huzmo/HuzDSP/Firmware/Drivers/lvgl-release-v9.5/docs/src/_static/images/clip_corner_3_layers_created.png

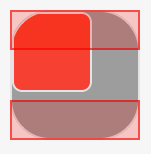
Firmware/Drivers/lvgl-release-v9.5/docs/src/_static/images/clip_corner_3_layers_created.png
