huzmo/HuzDSP/Firmware/Drivers/lvgl-release-v9.5/docs/src/_static/images/editor_initial_ui.png

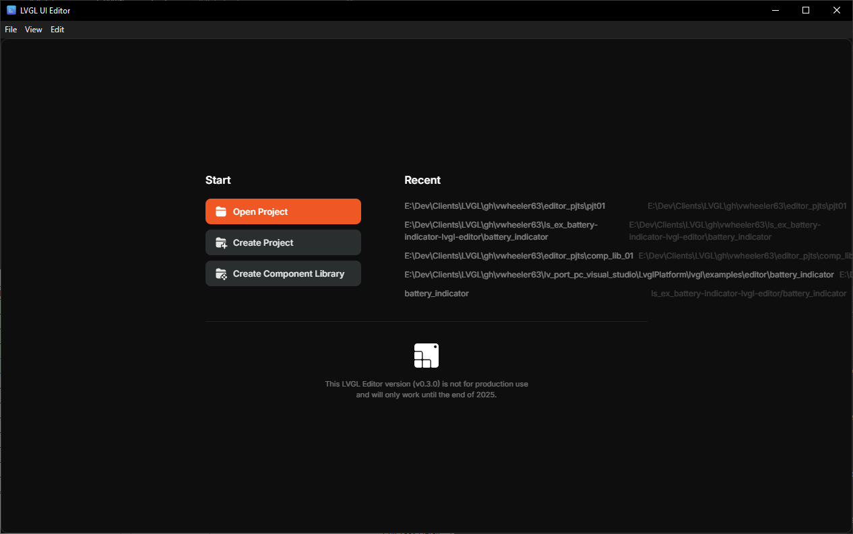
Firmware/Drivers/lvgl-release-v9.5/docs/src/_static/images/editor_initial_ui.png
