huzmo/HuzDSP/Firmware/Drivers/lvgl-release-v9.5/docs/src/_static/images/figma_to_lvgl_menu.png

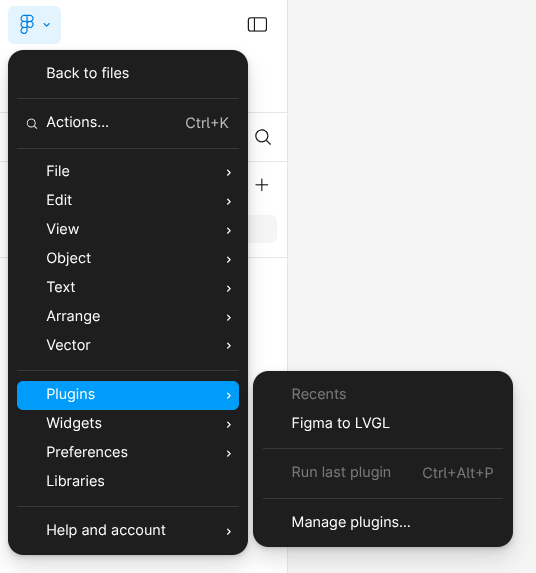
Firmware/Drivers/lvgl-release-v9.5/docs/src/_static/images/figma_to_lvgl_menu.png
