huzmo/HuzDSP/Firmware/Drivers/lvgl-release-v9.5/docs/src/_static/images/figma_to_lvgl_plugin.png

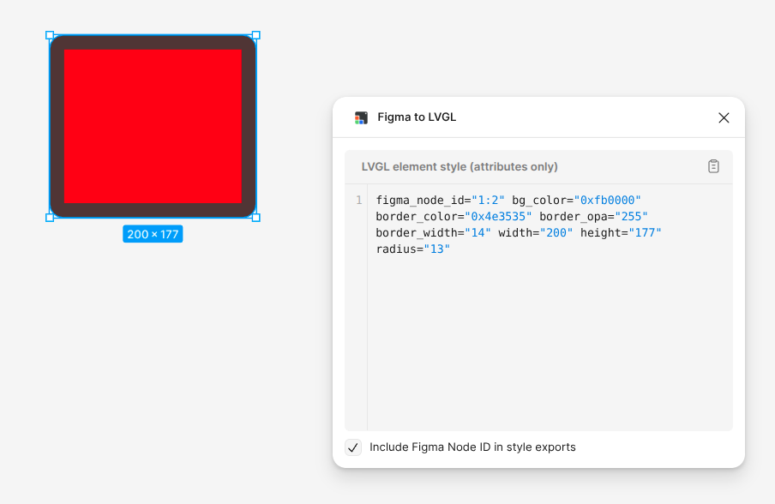
Firmware/Drivers/lvgl-release-v9.5/docs/src/_static/images/figma_to_lvgl_plugin.png
