huzmo/HuzDSP/Firmware/Drivers/lvgl-release-v9.5/docs/src/_static/images/gh-header.webp

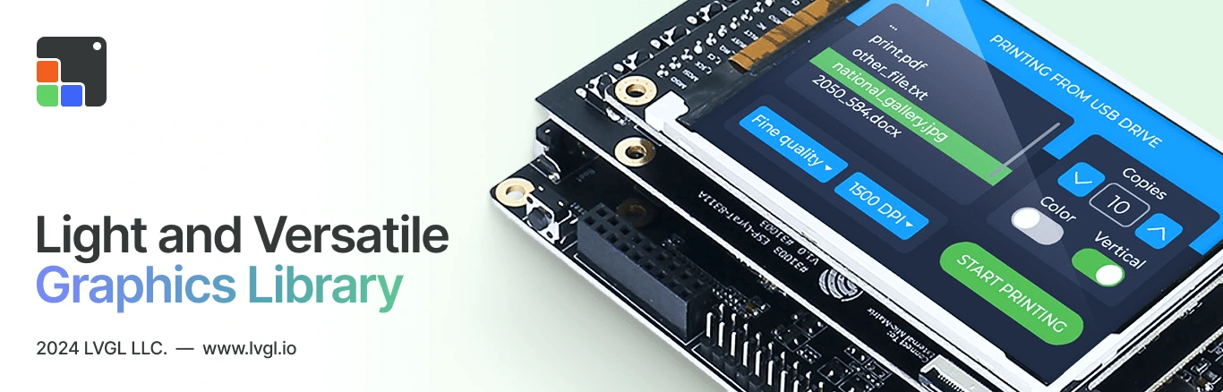
Firmware/Drivers/lvgl-release-v9.5/docs/src/_static/images/gh-header.webp
