huzmo/HuzDSP/Firmware/Drivers/lvgl-release-v9.5/docs/src/_static/images/home_1.png

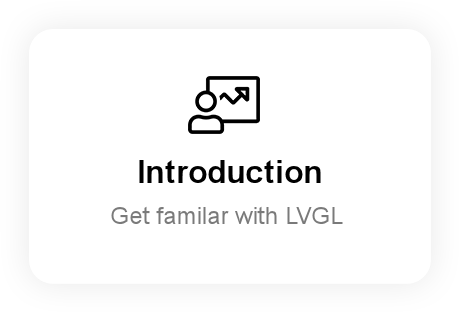
Firmware/Drivers/lvgl-release-v9.5/docs/src/_static/images/home_1.png
