huzmo/HuzDSP/Firmware/Drivers/lvgl-release-v9.5/docs/src/_static/images/home_3.png

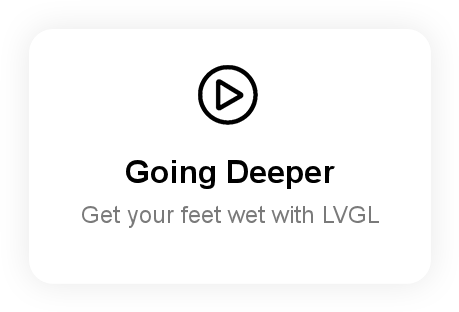
Firmware/Drivers/lvgl-release-v9.5/docs/src/_static/images/home_3.png
