huzmo/HuzDSP/Firmware/Drivers/lvgl-release-v9.5/docs/src/_static/images/intro_data_flow.png

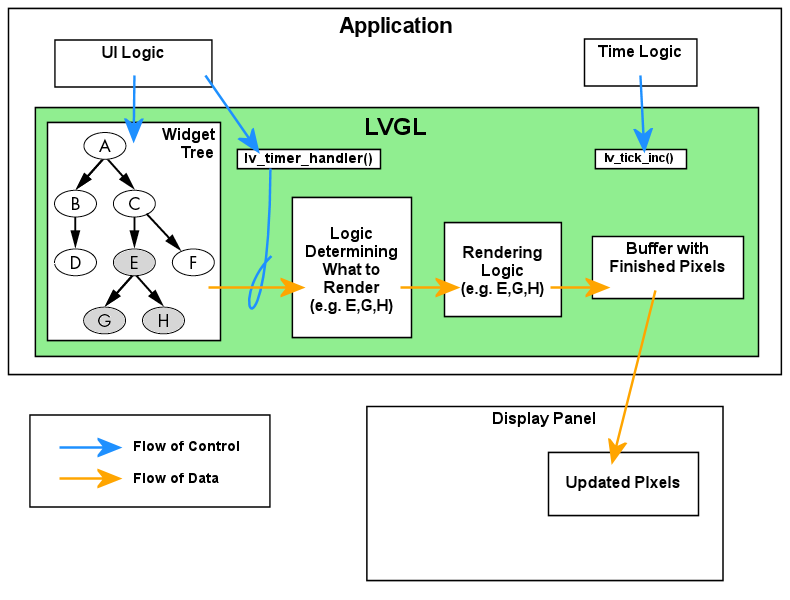
Firmware/Drivers/lvgl-release-v9.5/docs/src/_static/images/intro_data_flow.png
