huzmo/HuzDSP/Firmware/Drivers/lvgl-release-v9.5/docs/src/_static/images/lz4-compress-statistics.png

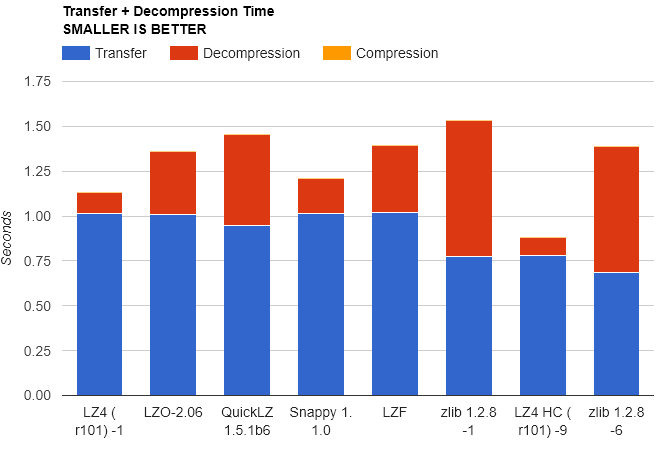
Firmware/Drivers/lvgl-release-v9.5/docs/src/_static/images/lz4-compress-statistics.png
