huzmo/HuzDSP/Firmware/Drivers/lvgl-release-v9.5/docs/src/_static/images/perfetto_ui.png

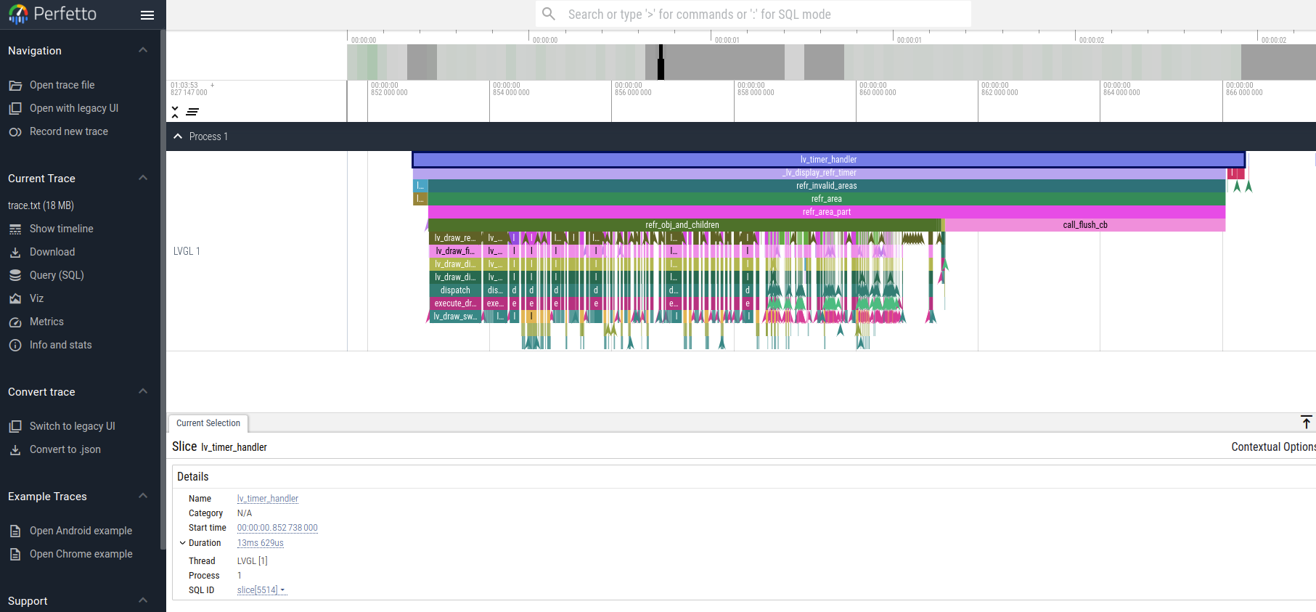
Firmware/Drivers/lvgl-release-v9.5/docs/src/_static/images/perfetto_ui.png
