huzmo/HuzDSP/Firmware/Drivers/lvgl-release-v9.5/docs/src/_static/images/renesas/generate.png

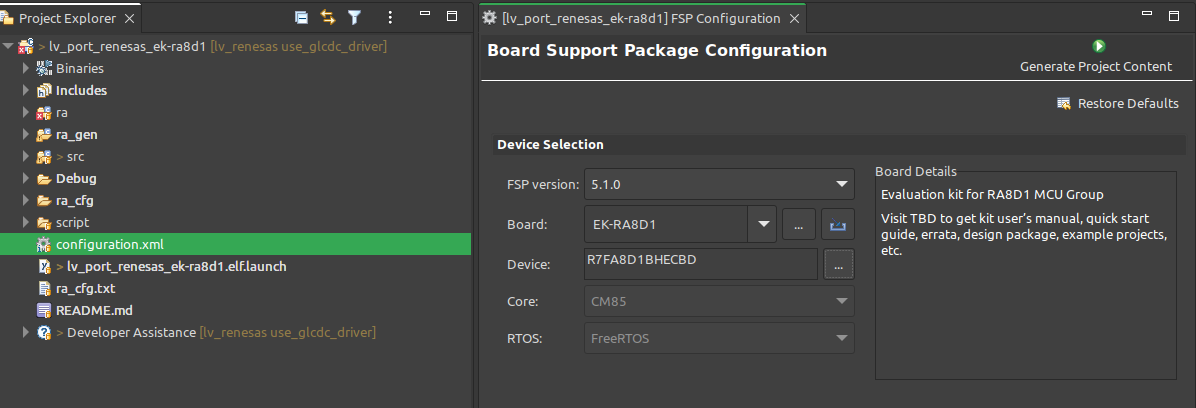
Firmware/Drivers/lvgl-release-v9.5/docs/src/_static/images/renesas/generate.png
