huzmo/HuzDSP/Firmware/Drivers/lvgl-release-v9.5/docs/src/_static/images/renesas/toolchains.png

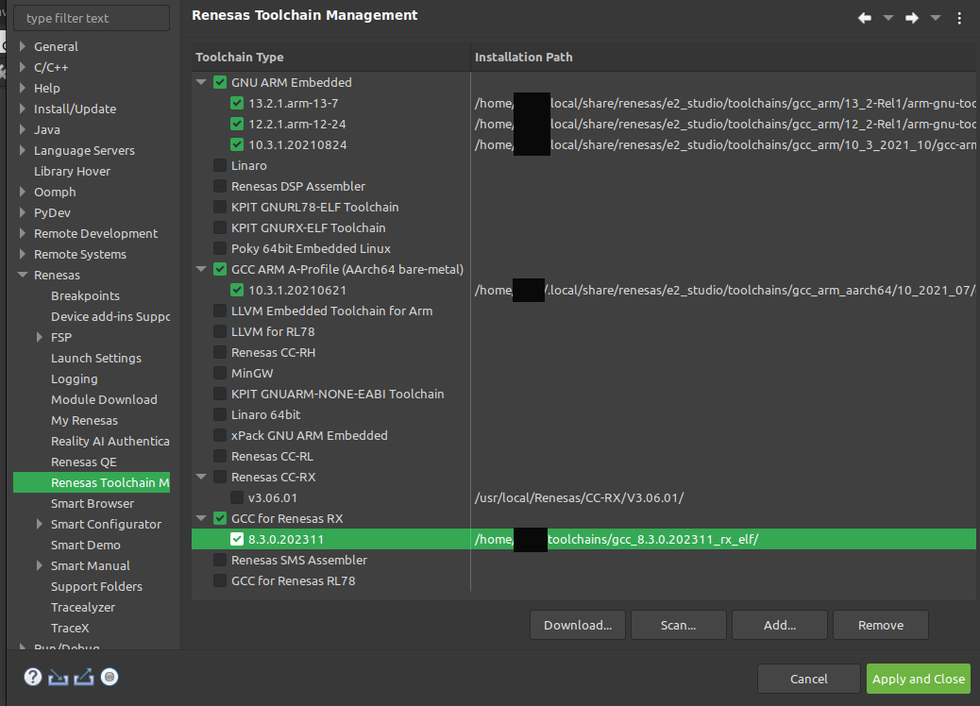
Firmware/Drivers/lvgl-release-v9.5/docs/src/_static/images/renesas/toolchains.png
