huzmo/HuzDSP/Firmware/Drivers/lvgl-release-v9.5/docs/src/_static/images/scale_ticks_below.png

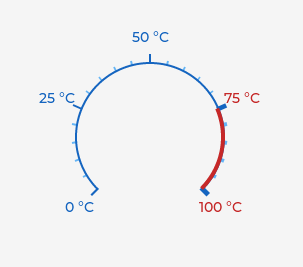
Firmware/Drivers/lvgl-release-v9.5/docs/src/_static/images/scale_ticks_below.png
