huzmo/HuzDSP/Firmware/Drivers/lvgl-release-v9.5/docs/src/_static/images/stm32cubemx-ltdc-fbaddr.png

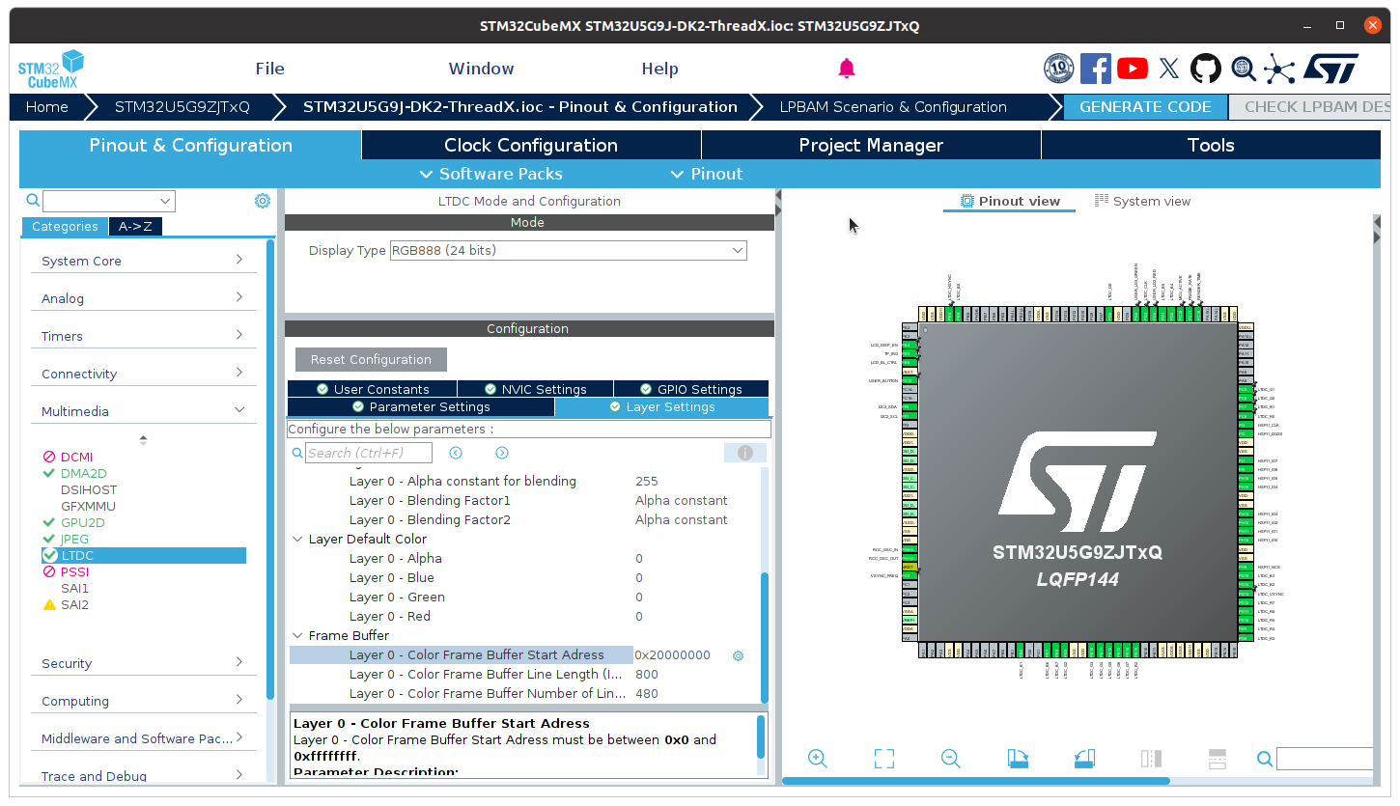
Firmware/Drivers/lvgl-release-v9.5/docs/src/_static/images/stm32cubemx-ltdc-fbaddr.png
