huzmo/HuzDSP/Firmware/Core/Src/ili9488.c

/*
 * ili9488.c - OPTIMIZED VERSION
 *
 *  Created on: Dec 14, 2021
 *      Author: timagr615
 *  Optimized: Feb 2026
 */
#include "ili9488.h"

extern SPI_HandleTypeDef hspi1;

static uint8_t rotationNum=1;
static bool _cp437    = false;
static SPI_HandleTypeDef lcdSPIhandle;
//Chip Select pin
static GPIO_TypeDef  *tftCS_GPIO;
static uint16_t tftCS_PIN;
//Data Command pin
static GPIO_TypeDef  *tftDC_GPIO;
static uint16_t tftDC_PIN;
//Reset pin
static GPIO_TypeDef  *tftRESET_GPIO;
static uint16_t tftRESET_PIN;
uint16_t width;
uint16_t height;

static //Text simple font array (You can your own font)
const unsigned char font1[] = {
	0x00, 0x00, 0x00, 0x00, 0x00,
	0x3E, 0x5B, 0x4F, 0x5B, 0x3E,
	0x3E, 0x6B, 0x4F, 0x6B, 0x3E,
	0x1C, 0x3E, 0x7C, 0x3E, 0x1C,
	0x18, 0x3C, 0x7E, 0x3C, 0x18,
	0x1C, 0x57, 0x7D, 0x57, 0x1C,
	0x1C, 0x5E, 0x7F, 0x5E, 0x1C,
	0x00, 0x18, 0x3C, 0x18, 0x00,
	0xFF, 0xE7, 0xC3, 0xE7, 0xFF,
	0x00, 0x18, 0x24, 0x18, 0x00,
	0xFF, 0xE7, 0xDB, 0xE7, 0xFF,
	0x30, 0x48, 0x3A, 0x06, 0x0E,
	0x26, 0x29, 0x79, 0x29, 0x26,
	0x40, 0x7F, 0x05, 0x05, 0x07,
	0x40, 0x7F, 0x05, 0x25, 0x3F,
	0x5A, 0x3C, 0xE7, 0x3C, 0x5A,
	0x7F, 0x3E, 0x1C, 0x1C, 0x08,
	0x08, 0x1C, 0x1C, 0x3E, 0x7F,
	0x14, 0x22, 0x7F, 0x22, 0x14,
	0x5F, 0x5F, 0x00, 0x5F, 0x5F,
	0x06, 0x09, 0x7F, 0x01, 0x7F,
	0x00, 0x66, 0x89, 0x95, 0x6A,
	0x60, 0x60, 0x60, 0x60, 0x60,
	0x94, 0xA2, 0xFF, 0xA2, 0x94,
	0x08, 0x04, 0x7E, 0x04, 0x08,
	0x10, 0x20, 0x7E, 0x20, 0x10,
	0x08, 0x08, 0x2A, 0x1C, 0x08,
	0x08, 0x1C, 0x2A, 0x08, 0x08,
	0x1E, 0x10, 0x10, 0x10, 0x10,
	0x0C, 0x1E, 0x0C, 0x1E, 0x0C,
	0x30, 0x38, 0x3E, 0x38, 0x30,
	0x06, 0x0E, 0x3E, 0x0E, 0x06,
	0x00, 0x00, 0x00, 0x00, 0x00,
	0x00, 0x00, 0x5F, 0x00, 0x00,
	0x00, 0x07, 0x00, 0x07, 0x00,
	0x14, 0x7F, 0x14, 0x7F, 0x14,
	0x24, 0x2A, 0x7F, 0x2A, 0x12,
	0x23, 0x13, 0x08, 0x64, 0x62,
	0x36, 0x49, 0x56, 0x20, 0x50,
	0x00, 0x08, 0x07, 0x03, 0x00,
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
};

//***** Functions prototypes *****//

void SendByte(uint8_t data)
{
  SPI1->TXDR = data;
}

//1. Write Command to LCD
void ILI9488_SendCommand(uint8_t com)
{
	uint8_t tmpCmd = com;
	DC_COMMAND();
	CS_A();
	HAL_SPI_Transmit(&hspi1, &tmpCmd, 1, 1);
	CS_D();
}

//2. Write data to LCD
void ILI9488_SendData(uint8_t data)
{
	uint8_t tmpCmd = data;
	DC_DATA();
	CS_A();
	HAL_SPI_Transmit(&hspi1, &tmpCmd, 1, 1);
	CS_D();
}

//2.2 Write multiple/DMA - OPTIMIZED
void ILI9488_SendData_Multi(uint8_t *buff, size_t buff_size)
{
	DC_DATA();
	CS_A();
	while (buff_size > 0){
		uint16_t chunk_size = buff_size > 32768 ? 32768 : buff_size;
		HAL_SPI_Transmit(&hspi1, buff, chunk_size, HAL_MAX_DELAY);
		buff += chunk_size;
		buff_size -= chunk_size;
	}
	CS_D();
}

void WaitLastData()
{
	while(!(SPI1->SR & SPI_SR_TXTF));
	while(SPI1->SR & SPI_SR_UDR);
}

void ILI9488_Init()
{
	CS_D();
	RST_A();
	HAL_Delay(10);
	RST_D();

	width = ILI9488_TFTWIDTH;
	height = ILI9488_TFTHEIGHT;

	ILI9488_SendCommand(0xE0);
	ILI9488_SendData(0x00);
	ILI9488_SendData(0x03);
	ILI9488_SendData(0x09);
	ILI9488_SendData(0x08);
	ILI9488_SendData(0x16);
	ILI9488_SendData(0x0A);
	ILI9488_SendData(0x3F);
	ILI9488_SendData(0x78);
	ILI9488_SendData(0x4C);
	ILI9488_SendData(0x09);
	ILI9488_SendData(0x0A);
	ILI9488_SendData(0x08);
	ILI9488_SendData(0x16);
	ILI9488_SendData(0x1A);
	ILI9488_SendData(0x0F);

	ILI9488_SendCommand(0XE1);
	ILI9488_SendData(0x00);
	ILI9488_SendData(0x16);
	ILI9488_SendData(0x19);
	ILI9488_SendData(0x03);
	ILI9488_SendData(0x0F);
	ILI9488_SendData(0x05);
	ILI9488_SendData(0x32);
	ILI9488_SendData(0x45);
	ILI9488_SendData(0x46);
	ILI9488_SendData(0x04);
	ILI9488_SendData(0x0E);
	ILI9488_SendData(0x0D);
	ILI9488_SendData(0x35);
	ILI9488_SendData(0x37);
	ILI9488_SendData(0x0F);

	ILI9488_SendCommand(0XC0);      //Power Control 1
	ILI9488_SendData(0x17);    //Vreg1out
	ILI9488_SendData(0x15);    //Verg2out

	ILI9488_SendCommand(0xC1);      //Power Control 2
	ILI9488_SendData(0x41);    //VGH,VGL

	ILI9488_SendCommand(0xC5);      //Power Control 3
	ILI9488_SendData(0x00);
	ILI9488_SendData(0x12);    //Vcom
	ILI9488_SendData(0x80);

	ILI9488_SendCommand(0x36);      //Memory Access
	ILI9488_SendData(0x48);

	ILI9488_SendCommand(0x3A);      // Interface Pixel Format
	ILI9488_SendData(0x66); 	  //18 bit

	ILI9488_SendCommand(0XB0);      // Interface Mode Control
	ILI9488_SendData(0x80);     			 //SDO NOT USE

	ILI9488_SendCommand(0xB1);      //Frame rate
	ILI9488_SendData(0xA0);    //60Hz

	ILI9488_SendCommand(0xB4);      //Display Inversion Control
	ILI9488_SendData(0x02);    //2-dot

	ILI9488_SendCommand(0XB6); //Display Function Control  RGB/MCU Interface Control
	ILI9488_SendData(0x02);    //MCU
	ILI9488_SendData(0x02);    //Source,Gate scan dieection

	ILI9488_SendCommand(0XE9);      // Set Image Functio
	ILI9488_SendData(0x00);    // Disable 24 bit data

	ILI9488_SendCommand(0xF7);      // Adjust Control
	ILI9488_SendData(0xA9);
	ILI9488_SendData(0x51);
	ILI9488_SendData(0x2C);
	ILI9488_SendData(0x82);    // D7 stream, loose

	//ILI9488_SendData(0x36);
	//ILI9488_SendData(0x08);
	setRotation(1);

	ILI9488_SendCommand(ILI9488_SLPOUT);    //Exit Sleep
	HAL_Delay(120);
	ILI9488_SendCommand(ILI9488_DISPON);    //Display on
}

void setAddrWindow(uint16_t x0, uint16_t y0, uint16_t x1, uint16_t y1)
{
	ILI9488_SendCommand(ILI9488_CASET); // Column addr set
	{
		uint8_t data[] = {(x0 >> 8) & 0xFF, x0 & 0xFF, (x1 >> 8) & 0xFF, x1 & 0xFF};
		ILI9488_SendData_Multi(data, sizeof(data));
	}
	ILI9488_SendCommand(ILI9488_PASET); // Row addr set
	{
		uint8_t data[] = {(y0 >> 8) & 0xFF, y0 & 0xFF, (y1 >> 8) & 0xFF, y1 & 0xFF};
		ILI9488_SendData_Multi(data, sizeof(data));
	}
	ILI9488_SendCommand(ILI9488_RAMWR); // write to RAM
}

void setScrollArea(uint16_t topFixedArea, uint16_t bottomFixedArea)
{
	ILI9488_SendCommand(0x33); // Vertical scroll definition
	ILI9488_SendData(topFixedArea >> 8);
	ILI9488_SendData(topFixedArea);
	ILI9488_SendData((height - topFixedArea - bottomFixedArea) >> 8);
	ILI9488_SendData(height - topFixedArea - bottomFixedArea);
	ILI9488_SendData(bottomFixedArea >> 8);
	ILI9488_SendData(bottomFixedArea);
}

void scroll(uint16_t pixels)
{
	ILI9488_SendCommand(0x37); // Vertical scrolling start address
	ILI9488_SendData(pixels >> 8);
	ILI9488_SendData(pixels);
}

void pushColor(uint16_t color)
{
	HAL_GPIO_WritePin(tftDC_GPIO, tftDC_PIN, GPIO_PIN_SET);
	HAL_GPIO_WritePin(tftCS_GPIO, tftCS_PIN, GPIO_PIN_RESET);
	write16BitColor(color);
	HAL_GPIO_WritePin(tftCS_GPIO, tftCS_PIN, GPIO_PIN_SET);
}

void pushColors(uint16_t *data, uint8_t len, uint8_t first)
{
	uint16_t color;
	uint8_t buff[len * 3 + 1];
	uint16_t count = 0;
	uint8_t lencount = len;
	HAL_GPIO_WritePin(tftCS_GPIO, tftCS_PIN, GPIO_PIN_RESET);

	if (first == 1) {
		HAL_GPIO_WritePin(tftDC_GPIO, tftDC_PIN, GPIO_PIN_SET);
	}
	while (lencount--)
	{
		color = *data++;
		buff[count] = (((color & 0xF800) >> 11) * 255) / 31;
		count++;
		buff[count] = (((color & 0x07E0) >> 5) * 255) / 63;
		count++;
		buff[count] = ((color & 0x001F) * 255) / 31;
		count++;
	}
	HAL_SPI_Transmit(&lcdSPIhandle, buff, len * 3, 100);
	HAL_GPIO_WritePin(tftCS_GPIO, tftCS_PIN, GPIO_PIN_SET);
}

void drawImage(const uint8_t* img, uint16_t x, uint16_t y, uint16_t w, uint16_t h)
{
    if ((x >= width) || (y >= height))
        return;
    if ((x + w - 1) >= width)
        w = width - x;
    if ((y + h - 1) >= height)
        h = height - y;

    setAddrWindow(x, y, x + w - 1, y + h - 1);

    // Convert entire image at once
    uint32_t total_pixels = (uint32_t)w * (uint32_t)h;
    uint32_t buffer_size = total_pixels * 3;  // RGB888 format

    // Allocate buffer (or use static if size is known)
    uint8_t *buffer = malloc(buffer_size);
    if (!buffer) return;  // Handle allocation failure

    uint32_t buf_idx = 0;
    uint32_t img_idx = 0;

    // Convert RGB565 to RGB888 in one pass
    for (uint32_t i = 0; i < total_pixels; i++) {
        uint8_t b1 = img[img_idx++];
        uint8_t b2 = img[img_idx++];
        uint16_t color = (b1 << 8) | b2;

        buffer[buf_idx++] = ((color & 0xF800) >> 11) * 255 / 31;  // R
        buffer[buf_idx++] = ((color & 0x07E0) >> 5) * 255 / 63;   // G
        buffer[buf_idx++] = (color & 0x001F) * 255 / 31;           // B
    }

    // Send entire image in one transaction
    ILI9488_SendData_Multi(buffer, buffer_size);

    free(buffer);
}

void drawPixel(int16_t x, int16_t y, uint16_t color)
{
	if ((x < 0) || (x >= width) || (y < 0) || (y >= height))
		return;

	setAddrWindow(x, y, x + 1, y + 1);
	HAL_GPIO_WritePin(tftDC_GPIO, tftDC_PIN, GPIO_PIN_SET);
	HAL_GPIO_WritePin(tftCS_GPIO, tftCS_PIN, GPIO_PIN_RESET);
	write16BitColor(color);
	HAL_GPIO_WritePin(tftCS_GPIO, tftCS_PIN, GPIO_PIN_SET);
}

void drawFastVLine(int16_t x, int16_t y, int16_t h, uint16_t color)
{
	if ((x >= width) || (y >= height))
		return;

	if ((y + h - 1) >= height)
		h = height - y;

	setAddrWindow(x, y, x, y + h - 1);
	HAL_GPIO_WritePin(tftDC_GPIO, tftDC_PIN, GPIO_PIN_SET);
	HAL_GPIO_WritePin(tftCS_GPIO, tftCS_PIN, GPIO_PIN_RESET);

	while (h--) {
		write16BitColor(color);
	}
	HAL_GPIO_WritePin(tftCS_GPIO, tftCS_PIN, GPIO_PIN_SET);
}

void drawFastHLine(int16_t x, int16_t y, int16_t w, uint16_t color)
{
	if ((x >= width) || (y >= height))
		return;
	if ((x + w - 1) >= width)
		w = width - x;
	setAddrWindow(x, y, x + w - 1, y);
	HAL_GPIO_WritePin(tftDC_GPIO, tftDC_PIN, GPIO_PIN_SET);
	HAL_GPIO_WritePin(tftCS_GPIO, tftCS_PIN, GPIO_PIN_RESET);
	while (w--)
	{
		write16BitColor(color);
	}
	HAL_GPIO_WritePin(tftCS_GPIO, tftCS_PIN, GPIO_PIN_SET);
}

void drawLine(int16_t x0, int16_t y0, int16_t x1, int16_t y1, uint16_t color)
{
	if (x0 == x1) {
		if (y0 > y1)
			swap(y0, y1);
		drawFastVLine(x0, y0, y1 - y0 + 1, color);
	} else if (y0 == y1) {
		if (x0 > x1)
			swap(x0, x1);
		drawFastHLine(x0, y0, x1 - x0 + 1, color);
	} else {
		writeLine(x0, y0, x1, y1, color);
	}
}

void writeLine(int16_t x0, int16_t y0, int16_t x1, int16_t y1, uint16_t color)
{
	int16_t steep = abs(y1 - y0) > abs(x1 - x0);
	if (steep) {
		swap(x0, y0);
		swap(x1, y1);
	}

	if (x0 > x1) {
		swap(x0, x1);
		swap(y0, y1);
	}

	int16_t dx, dy;
	dx = x1 - x0;
	dy = abs(y1 - y0);

	int16_t err = dx / 2;
	int16_t ystep;

	if (y0 < y1) {
		ystep = 1;
	} else {
		ystep = -1;
	}

	for (; x0 <= x1; x0++) {
		if (steep) {
			drawPixel(y0, x0, color);
		} else {
			drawPixel(x0, y0, color);
		}
		err -= dy;
		if (err < 0) {
			y0 += ystep;
			err += dx;
		}
	}
}

//6. Fill the entire screen with a background color - OPTIMIZED
void fillScreen(uint16_t color)
{
	fillRect(0, 0, width, height, color);
}

// OPTIMIZED fillRect - Uses fixed buffer size for better performance
#define FILL_CHUNK_SIZE 1024

void fillRect(int16_t x, int16_t y, int16_t w, int16_t h, uint16_t color)
{
	if ((x >= width) || (y >= height))
		return;
	if ((x + w - 1) >= width)
		w = width - x;
	if ((y + h - 1) >= height)
		h = height - y;

	setAddrWindow(x, y, x + w - 1, y + h - 1);

	uint8_t r = ((color & 0xF800) >> 11) * 255 / 31;
	uint8_t g = ((color & 0x07E0) >> 5) * 255 / 63;
	uint8_t b = (color & 0x001F) * 255 / 31;

	// Use fixed buffer size for better performance
	static uint8_t buffer[FILL_CHUNK_SIZE * 3];

	// Fill buffer with color pattern
	for (uint16_t i = 0; i < FILL_CHUNK_SIZE; i++) {
		buffer[i*3] = r;
		buffer[i*3+1] = g;
		buffer[i*3+2] = b;
	}

	uint32_t total_pixels = (uint32_t)w * (uint32_t)h;
	DC_DATA();
	CS_A();

	while(total_pixels > 0) {
		uint32_t chunk = (total_pixels > FILL_CHUNK_SIZE) ? FILL_CHUNK_SIZE : total_pixels;
		HAL_SPI_Transmit(&hspi1, buffer, chunk * 3, HAL_MAX_DELAY);
		total_pixels -= chunk;
	}

	CS_D();
}

void setRotation(uint8_t r)
{
	ILI9488_SendCommand(ILI9488_MADCTL);
	uint8_t rotation = r % 4; // can't be higher than 3
	switch (rotation) {
	case 0:
		ILI9488_SendData(MADCTL_MX | MADCTL_BGR);
		width = ILI9488_TFTWIDTH;
		height = ILI9488_TFTHEIGHT;
		break;
	case 1:
		ILI9488_SendData(MADCTL_MV | MADCTL_BGR);
		width = ILI9488_TFTHEIGHT;
		height = ILI9488_TFTWIDTH;
		break;
	case 2:
		ILI9488_SendData(MADCTL_MY | MADCTL_BGR);
		width = ILI9488_TFTWIDTH;
		height = ILI9488_TFTHEIGHT;
		break;
	case 3:
		ILI9488_SendData(MADCTL_MX | MADCTL_MY | MADCTL_MV | MADCTL_BGR);
		width = ILI9488_TFTHEIGHT;
		height = ILI9488_TFTWIDTH;
		break;
	}
}

void invertDisplay(uint8_t i)
{
	ILI9488_SendCommand(i ? ILI9488_INVON : ILI9488_INVOFF);
}

uint16_t color565(uint8_t r, uint8_t g, uint8_t b)
{
	return ((r & 0xF8) << 8) | ((g & 0xFC) << 3) | (b >> 3);
}

// OPTIMIZED drawChar - Buffers entire character before sending
void drawChar(int16_t x, int16_t y, unsigned char c, uint16_t color, uint16_t bg, uint8_t size)
{
	if(rotationNum == 1 || rotationNum == 3)
	{
		if((x >= ILI9488_TFTWIDTH) || (y >= ILI9488_TFTHEIGHT) ||
		   ((x + 6 * size - 1) < 0) || ((y + 8 * size - 1) < 0))
			return;
	}
	else
	{
		if((y >= ILI9488_TFTWIDTH) || (x >= ILI9488_TFTHEIGHT) ||
		   ((y + 6 * size - 1) < 0) || ((x + 8 * size - 1) < 0))
			return;
	}

	if(!_cp437 && (c >= 176)) c++; // Handle 'classic' charset behavior

	// Character dimensions
	uint16_t char_width = 6 * size;
	uint16_t char_height = 8 * size;

	// Create buffer for entire character
	uint8_t buffer[char_width * char_height * 3];
	uint16_t buf_idx = 0;

	// Extract color components once
	uint8_t r_fg = ((color & 0xF800) >> 11) * 255 / 31;
	uint8_t g_fg = ((color & 0x07E0) >> 5) * 255 / 63;
	uint8_t b_fg = (color & 0x001F) * 255 / 31;

	uint8_t r_bg = ((bg & 0xF800) >> 11) * 255 / 31;
	uint8_t g_bg = ((bg & 0x07E0) >> 5) * 255 / 63;
	uint8_t b_bg = (bg & 0x001F) * 255 / 31;

	// Build character buffer row by row
	for (int8_t j = 0; j < 8; j++) {
		for (int8_t sy = 0; sy < size; sy++) {
			for (int8_t i = 0; i < 6; i++) {
				uint8_t line;
				if (i == 5)
					line = 0x0;
				else
					line = pgm_read_byte(font1 + (c * 5) + i);

				bool pixel_on = line & (1 << j);

				for (int8_t sx = 0; sx < size; sx++) {
					if (pixel_on) {
						buffer[buf_idx++] = r_fg;
						buffer[buf_idx++] = g_fg;
						buffer[buf_idx++] = b_fg;
					} else {
						buffer[buf_idx++] = r_bg;
						buffer[buf_idx++] = g_bg;
						buffer[buf_idx++] = b_bg;
					}
				}
			}
		}
	}

	// Send entire character in one transaction
	setAddrWindow(x, y, x + char_width - 1, y + char_height - 1);
	ILI9488_SendData_Multi(buffer, buf_idx);
}

// OPTIMIZED text printing - uses optimized drawChar
void ILI9488_printText(char text[], int16_t x, int16_t y, uint16_t color, uint16_t bg, uint8_t size)
{
	int16_t offset = size * 6;

	for(uint16_t i = 0; i < 40 && text[i] != '\0'; i++)
	{
		drawChar(x + (offset * i), y, text[i], color, bg, size);
	}
}

void testLines(uint8_t color)
{
	//unsigned long start, t;
	int x1, y1, x2, y2, w = width, h = height;
	fillScreen(ILI9488_BLACK);

	x1 = y1 = 0;
	y2 = h - 1;

	for (x2 = 0; x2 < w; x2 += 6)
		drawLine(x1, y1, x2, y2, color);
	x2 = w - 1;
	for (y2 = 0; y2 < h; y2 += 6)
		drawLine(x1, y1, x2, y2, color);
	fillScreen(ILI9488_BLACK);

	x1 = w - 1;
	y1 = 0;
	y2 = h - 1;

	for (x2 = 0; x2 < w; x2 += 6)
		drawLine(x1, y1, x2, y2, color);
	x2 = 0;
	for (y2 = 0; y2 < h; y2 += 6)
		drawLine(x1, y1, x2, y2, color);

	fillScreen(ILI9488_BLACK);

	x1 = 0;
	y1 = h - 1;
	y2 = 0;

	for (x2 = 0; x2 < w; x2 += 6)
		drawLine(x1, y1, x2, y2, color);
	x2 = w - 1;
	for (y2 = 0; y2 < h; y2 += 6)
		drawLine(x1, y1, x2, y2, color);

	fillScreen(ILI9488_BLACK);

	x1 = w - 1;
	y1 = h - 1;
	y2 = 0;

	for (x2 = 0; x2 < w; x2 += 6)
		drawLine(x1, y1, x2, y2, color);
	x2 = 0;
	for (y2 = 0; y2 < h; y2 += 6)
		drawLine(x1, y1, x2, y2, color);
}

void write16BitColor(uint16_t color)
{
	uint8_t r = ((color & 0xF800) >> 11) * 255 / 31;
	uint8_t g = ((color & 0x07E0) >> 5) * 255 / 63;
	uint8_t b = (color & 0x001F) * 255 / 31;
	uint8_t data[3] = {r, g, b};
	ILI9488_SendData_Multi(data, 3);
}

// Draw rectangle outline
void drawRect(int16_t x, int16_t y, int16_t w, int16_t h, uint16_t color)
{
    drawFastHLine(x, y, w, color);           // Top
    drawFastHLine(x, y + h - 1, w, color);   // Bottom
    drawFastVLine(x, y, h, color);           // Left
    drawFastVLine(x + w - 1, y, h, color);   // Right
}

// Draw filled circle (Bresenham's algorithm)
void fillCircle(int16_t x0, int16_t y0, int16_t r, uint16_t color)
{
    int16_t f = 1 - r;
    int16_t ddF_x = 1;
    int16_t ddF_y = -2 * r;
    int16_t x = 0;
    int16_t y = r;

    drawFastHLine(x0 - r, y0, 2 * r + 1, color);

    while (x < y) {
        if (f >= 0) {
            y--;
            ddF_y += 2;
            f += ddF_y;
        }
        x++;
        ddF_x += 2;
        f += ddF_x;

        drawFastHLine(x0 - x, y0 + y, 2 * x + 1, color);
        drawFastHLine(x0 - x, y0 - y, 2 * x + 1, color);
        drawFastHLine(x0 - y, y0 + x, 2 * y + 1, color);
        drawFastHLine(x0 - y, y0 - x, 2 * y + 1, color);
    }
}
