huzmo/HuzDSP/Firmware/Core/Inc/ili9488.h

/*
 * ili9488.h
 *
 *  Created on: Dec 14, 2021
 *      Author: timagr615
 */

#ifndef INC_ILI9488_H_
#define INC_ILI9488_H_

#include <math.h>
#include <stdbool.h>
//** CHANGE BASED ON STM32 CHIP F4/F7/F1...**//
#include "stm32h7xx_hal.h"
#include "main.h"
#include <stdlib.h>
#include <stdio.h>
#include <string.h>

#define LCD_WIDTH 480
#define LCD_HEIGHT 320

#define RST_A() HAL_GPIO_WritePin(TFT_RST_GPIO_Port,TFT_RST_Pin,GPIO_PIN_RESET)
#define RST_D() HAL_GPIO_WritePin(TFT_RST_GPIO_Port,TFT_RST_Pin,GPIO_PIN_SET)
#define CS_A() HAL_GPIO_WritePin(TFT_CS_GPIO_Port,TFT_CS_Pin,GPIO_PIN_RESET)
#define CS_D() HAL_GPIO_WritePin(TFT_CS_GPIO_Port,TFT_CS_Pin,GPIO_PIN_SET)
#define DC_COMMAND() HAL_GPIO_WritePin(TFT_DC_GPIO_Port,TFT_DC_Pin,GPIO_PIN_RESET)
#define DC_DATA() HAL_GPIO_WritePin(TFT_DC_GPIO_Port,TFT_DC_Pin,GPIO_PIN_SET)

#define ILI9488_TFTWIDTH  480
#define ILI9488_TFTHEIGHT 320
#define ILI9488_PIXEL_COUNT	ILI9488_TFTWIDTH * ILI9488_TFTHEIGHT

#define ILI9488_NOP     0x00
#define ILI9488_SWRESET 0x01
#define ILI9488_RDDID   0x04
#define ILI9488_RDDST   0x09

#define ILI9488_SLPIN   0x10
#define ILI9488_SLPOUT  0x11
#define ILI9488_PTLON   0x12
#define ILI9488_NORON   0x13

#define ILI9488_RDMODE  0x0A
#define ILI9488_RDMADCTL  0x0B
#define ILI9488_RDPIXFMT  0x0C
#define ILI9488_RDIMGFMT  0x0D
#define ILI9488_RDSELFDIAG  0x0F

#define ILI9488_INVOFF  0x20
#define ILI9488_INVON   0x21
#define ILI9488_GAMMASET 0x26
#define ILI9488_DISPOFF 0x28
#define ILI9488_DISPON  0x29

#define ILI9488_CASET   0x2A
#define ILI9488_PASET   0x2B
#define ILI9488_RAMWR   0x2C
#define ILI9488_RAMRD   0x2E

#define ILI9488_PTLAR   0x30
#define ILI9488_MADCTL  0x36
#define ILI9488_PIXFMT  0x3A

#define ILI9488_FRMCTR1 0xB1
#define ILI9488_FRMCTR2 0xB2
#define ILI9488_FRMCTR3 0xB3
#define ILI9488_INVCTR  0xB4
#define ILI9488_DFUNCTR 0xB6

#define ILI9488_PWCTR1  0xC0
#define ILI9488_PWCTR2  0xC1
#define ILI9488_PWCTR3  0xC2
#define ILI9488_PWCTR4  0xC3
#define ILI9488_PWCTR5  0xC4
#define ILI9488_VMCTR1  0xC5
#define ILI9488_VMCTR2  0xC7

#define ILI9488_RDID1   0xDA
#define ILI9488_RDID2   0xDB
#define ILI9488_RDID3   0xDC
#define ILI9488_RDID4   0xDD

#define ILI9488_GMCTRP1 0xE0
#define ILI9488_GMCTRN1 0xE1
/*
#define ILI9488_PWCTR6  0xFC
*/

// Color definitions
#define ILI9488_BLACK      			0x0000      /*   0,   0,   0 */
#define ILI9488_NAVY				0x000F      /*   0,   0, 128 */
#define ILI9488_DARKGREEN   		0x03E0      /*   0, 128,   0 */
#define ILI9488_DARKCYAN    		0x03EF      /*   0, 128, 128 */
#define ILI9488_MAROON      		0x7800      /* 128,   0,   0 */
#define ILI9488_PURPLE      		0x780F      /* 128,   0, 128 */
#define ILI9488_OLIVE       			0x7BE0      /* 128, 128,   0 */
#define ILI9488_LIGHTGREY   		0xC618      /* 192, 192, 192 */
#define ILI9488_DARKGREY    		0x7BEF      /* 128, 128, 128 */
#define ILI9488_BLUE        			0x001F      /*   0,   0, 255 */
#define ILI9488_GREEN       		0x07E0      /*   0, 255,   0 */
#define ILI9488_CYAN        			0x07FF      /*   0, 255, 255 */
#define ILI9488_RED         			0xF800      /* 255,   0,   0 */
#define ILI9488_MAGENTA     		0xF81F      /* 255,   0, 255 */
#define ILI9488_YELLOW      		0xFFE0      /* 255, 255,   0 */
#define ILI9488_WHITE       			0xFFFF      /* 255, 255, 255 */
#define ILI9488_ORANGE      		0xFD20      /* 255, 165,   0 */
#define ILI9488_GREENYELLOW 	0xAFE5      /* 173, 255,  47 */
#define ILI9488_PINK        			0xF81F

#define	TFT9341_BLACK   0x0000
#define	TFT9341_BLUE    0x001F
#define	TFT9341_RED     0xF800
#define	TFT9341_GREEN   0x07E0
#define TFT9341_CYAN    0x07FF
#define TFT9341_MAGENTA 0xF81F
#define TFT9341_YELLOW  0xFFE0
#define TFT9341_WHITE   0xFFFF
#define MADCTL_MY  0x80
#define MADCTL_MX  0x40
#define MADCTL_MV  0x20
#define MADCTL_ML  0x10
#define MADCTL_RGB 0x00
#define MADCTL_BGR 0x08
#define MADCTL_MH  0x04


#define swap(a, b) { int16_t t = a; a = b; b = t; }
#define pgm_read_byte(addr) (*(const unsigned char *)(addr))
#define min(a,b) (((a)<(b))?(a):(b))

//***** Functions prototypes *****//
//1. Write Command to LCD
void ILI9341_SendCommand(uint8_t com);
//2. Write data to LCD
void ILI9341_SendData(uint8_t data);
//2.2 Write multiple/DMA
void ILI9488_SendData_Multi(uint8_t *buff, size_t buff_size);
void SendByte(uint8_t data);
void WaitLastData();
//void ILI9488_Init(SPI_HandleTypeDef *spiLcdHandle, GPIO_TypeDef *csPORT, uint16_t csPIN, GPIO_TypeDef *dcPORT, uint16_t dcPIN, GPIO_TypeDef *resetPORT, uint16_t resetPIN);
void ILI9488_Init();
void setAddrWindow(uint16_t x0, uint16_t y0, uint16_t x1, uint16_t y1);
void setScrollArea(uint16_t topFixedArea, uint16_t bottomFixedArea);
void scroll(uint16_t pixels);
void pushColor(uint16_t color);
void pushColors(uint16_t *data, uint8_t len, uint8_t first);
void drawImage(const uint8_t* img, uint16_t x, uint16_t y, uint16_t w, uint16_t h);
void fillScreen(uint16_t color);

void drawPixel(int16_t x, int16_t y, uint16_t color);
void drawFastVLine(int16_t x, int16_t y, int16_t h, uint16_t color);
void drawFastHLine(int16_t x, int16_t y, int16_t w, uint16_t color);
void drawLine(int16_t x0, int16_t y0, int16_t x1, int16_t y1,uint16_t color);
void writeLine(int16_t x0, int16_t y0, int16_t x1, int16_t y1,uint16_t color);
void fillRect(int16_t x, int16_t y, int16_t w, int16_t h, uint16_t color);
void drawRect(int16_t x, int16_t y, int16_t w, int16_t h, uint16_t color);
void fillCircle(int16_t x0, int16_t y0, int16_t r, uint16_t color);

void setRotation(uint8_t r);
void invertDisplay(uint8_t  i);
uint16_t color565(uint8_t r, uint8_t g, uint8_t b);
void drawChar(int16_t x, int16_t y, unsigned char c, uint16_t color, uint16_t bg, uint8_t size);
void ILI9488_printText(char text[], int16_t x, int16_t y, uint16_t color, uint16_t bg, uint8_t size);

void write16BitColor(uint16_t color);

void testLines(uint8_t color);


#endif /* INC_ILI9488_H_ */
